nostradomus/Base3-clock/images/RTC-clock-circuit.png

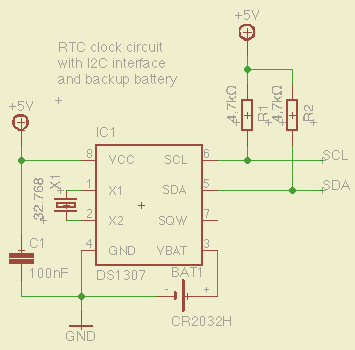
images/RTC-clock-circuit.png
